brer-rabbit/zoxnoxious/vcv_rack/src/Zoxnoxious5524.cpp

#include "TurnsCountingKnob.hpp"
#include "Zoxnoxious5524.hpp"

namespace zox {

// VCO1 ==> SSI2130
// VCO2 ==> AS3394

// these enums define the channel order being sent over the wire
enum cvChannel {
    // DAC AS3394 / chip select 0
    VCO_MIX = 0,
    VCO_TWO_PW,
    FINAL_GAIN,
    VCO_TWO_TRI_VCF,
    VCF_RESONANCE,
    VCO_ONE_MOD_AMOUNT,
    VCO_TWO_VOCT,
    VCF_CUTOFF,
    // DAC SSI2130 / SPI chip select 1
    VCO_ONE_TRIANGLE,
    VCO_ONE_LINEAR,
    VCO_ONE_VOCT,
    VCO_ONE_PW,
    VCO_TWO_WAVESHAPE_TZFM,
    VCO_TWO_MOD_AMOUNT,
    VCO_ONE_PULSE,
    VCO_ONE_SAW
};



Zoxnoxious5524::Zoxnoxious5524() : output1NameString(invalidCardOutputName),
                               output2NameString(invalidCardOutputName),
                               buttonMidiController(buttonMappings),
                               routes{{
    {VCO_ONE_SAW_KNOB_PARAM, VCO_ONE_SAW_INPUT, VCO_ONE_SAW, 10.f, &vcoOneSawClipTimer, nullptr, CvOperation::MultiplyNormalled},
    {VCO_ONE_PULSE_KNOB_PARAM, VCO_ONE_PULSE_INPUT, VCO_ONE_PULSE, 10.f, &vcoOnePulseClipTimer, nullptr, CvOperation::MultiplyNormalled},
    {VCO_TWO_MOD_AMOUNT_KNOB_PARAM, VCO_TWO_MOD_AMOUNT_INPUT, VCO_TWO_MOD_AMOUNT, 10.f, &vcoTwoModAmountClipTimer, nullptr, CvOperation::Add},
    {VCO_TWO_WAVESHAPE_TZFM_KNOB_PARAM, VCO_TWO_WAVESHAPE_TZFM_INPUT, VCO_TWO_WAVESHAPE_TZFM, 10.f, &vcoTwoWaveshapeTzfmClipTimer, nullptr, CvOperation::Add},
    {VCO_ONE_PW_KNOB_PARAM,VCO_ONE_PW_INPUT, VCO_ONE_PW, 10.f, &vcoOnePwClipTimer, nullptr, CvOperation::Add},
    {VCO_ONE_VOCT_KNOB_PARAM, VCO_ONE_VOCT_INPUT, VCO_ONE_VOCT, 8.f, &vcoOneVoctClipTimer, nullptr, CvOperation::Add},
    {VCO_ONE_LINEAR_KNOB_PARAM, VCO_ONE_LINEAR_INPUT, VCO_ONE_LINEAR, 10.f, &vcoOneLinearClipTimer, nullptr, CvOperation::Add},
    {VCO_ONE_TRIANGLE_KNOB_PARAM, VCO_ONE_TRIANGLE_INPUT, VCO_ONE_TRIANGLE, 10.f, &vcoOneTriangleClipTimer, nullptr, CvOperation::MultiplyNormalled},
    {VCF_CUTOFF_KNOB_PARAM,VCF_CUTOFF_INPUT, VCF_CUTOFF, 10.f, &vcfCutoffClipTimer, nullptr, CvOperation::Add},
    {VCO_TWO_VOCT_KNOB_PARAM, VCO_TWO_VOCT_INPUT, VCO_TWO_VOCT, 6.f, &vcoTwoVoctClipTimer, nullptr, CvOperation::Add},
    {VCO_ONE_MOD_AMOUNT_KNOB_PARAM, VCO_ONE_MOD_AMOUNT_INPUT, VCO_ONE_MOD_AMOUNT, 10.f, &vcoOneModAmountClipTimer, nullptr, CvOperation::Add},
    {VCF_RESONANCE_KNOB_PARAM, VCF_RESONANCE_INPUT, VCF_RESONANCE, 10.f, &vcfResonanceClipTimer, dualLinearSwitch0_8, CvOperation::Add},
    {VCO_TWO_TRI_VCF_KNOB_PARAM, VCO_TWO_TRI_VCF_INPUT, VCO_TWO_TRI_VCF, 10.f, &vcoTwoTriVcfClipTimer, nullptr, CvOperation::Add},
    {FINAL_GAIN_KNOB_PARAM, FINAL_GAIN_INPUT, FINAL_GAIN, 10.f, &finalGainClipTimer, nullptr, CvOperation::Add},
    {VCO_TWO_PW_KNOB_PARAM,VCO_TWO_PW_INPUT, VCO_TWO_PW, 10.f, &vcoTwoPwClipTimer, nullptr, CvOperation::Add},
    {VCO_MIX_KNOB_PARAM, VCO_MIX_INPUT, VCO_MIX, 10.f, &vcoMixClipTimer, nullptr, CvOperation::Add} }} {

  setParticipant(this);
  setLightEnum(LINK_STATUS_LIGHT);

  config(PARAMS_LEN, INPUTS_LEN, OUTPUTS_LEN, LIGHTS_LEN);
  configParam(VCO_ONE_VOCT_KNOB_PARAM, 0.f, 1.f, 0.5f, "Frequency", " V", 0.f, 8.f);
  configParam(VCO_ONE_PW_KNOB_PARAM, 0.f, 1.f, 0.5f, "Pulse Width", "%", 0.f, 100.f);
  configParam(VCO_ONE_LINEAR_KNOB_PARAM, 0.f, 1.f, 0.5f, "Linear Mod", " V", 0.f, 10.f -5.f);
  configParam(VCO_TWO_VOCT_KNOB_PARAM, 0.f, 1.f, 0.5f, "Frequency", " V", 0.f, 6.f);
  configParam(VCO_TWO_PW_KNOB_PARAM, 0.f, 1.f, 0.5f, "Pulse Width", "%", 0.f, 100.f);
  configParam(VCF_CUTOFF_KNOB_PARAM, 0.f, 1.f, 1.f, "Cutoff", " V", 0.f, 10.f, -1.f);
  configParam(VCF_RESONANCE_KNOB_PARAM, 0.f, 1.f, 0.f, "Resonance", "%", 0.f, 100.f);
  configParam(VCO_MIX_KNOB_PARAM, 0.f, 1.f, 0.5f, "VCO1/VCO2 Mix", "%", 0.f, 200.f, -100.f);
  configParam(FINAL_GAIN_KNOB_PARAM, 0.f, 1.f, 0.f, "Final VCA", "%", 0.f, 100.f);
  configParam(VCO_ONE_PULSE_KNOB_PARAM, 0.f, 1.f, 0.f, "Pulse Gain", "%", 0.f, 100.f);
  configParam(VCO_ONE_TRIANGLE_KNOB_PARAM, 0.f, 1.f, 1.f, "Tri Gain", "%", 0.f, 100.f);
  configParam(VCO_ONE_SAW_KNOB_PARAM, 0.f, 1.f, 0.f, "Saw Gain", "%", 0.f, 100.f);

  configParam(VCO_ONE_MOD_AMOUNT_KNOB_PARAM, 0.f, 1.f, 0.f, "Mod Amount", "%", 0.f, 100.f);
  configParam(VCO_TWO_MOD_AMOUNT_KNOB_PARAM, 0.f, 1.f, 0.f, "Mod Amount", "%", 0.f, 100.f);
  configParam(VCO_TWO_WAVESHAPE_TZFM_KNOB_PARAM, 0.f, 1.f, 0.f, "Waveshape TZFM", "%", 0.f, 100.f);
  configParam(VCO_TWO_TRI_VCF_KNOB_PARAM, 0.f, 1.f, 0.f, "Tri to VCF", "%", 0.f, 100.f);

  configSwitch(VCO_ONE_TO_EXP_FM_VCO_TWO_BUTTON_PARAM, 0.f, 1.f, 0.f, "VCO One to Exp FM VCO Two", {"Off", "On"});
  configSwitch(VCO_ONE_TO_WAVE_SELECT_VCO_TWO_BUTTON_PARAM, 0.f, 1.f, 0.f, "VCO One to Wave Select VCO Two", {"Off", "On"});

  configSwitch(VCO_TWO_TO_FREQ_VCO_ONE_BUTTON_PARAM, 0.f, 1.f, 0.f, "VCO Two to TZ-FM VCO One", {"Off", "On"});
  configSwitch(VCO_TWO_TO_SOFT_SYNC_VCO_ONE_BUTTON_PARAM, 0.f, 1.f, 0.f, "Soft Sync VCO One from VCO Two", {"Off", "On"});
  configSwitch(VCO_TWO_TO_HARD_SYNC_VCO_ONE_BUTTON_PARAM, 0.f, 1.f, 0.f, "Hard Sub Sync VCO One from VCO Two", {"Off", "On"});

  configSwitch(VCO_ONE_TO_PW_VCO_TWO_BUTTON_PARAM, 0.f, 1.f, 0.f, "VCO One to VCO Two Pulse Width", {"Off", "On"});
  configSwitch(VCO_ONE_TO_VCF_BUTTON_PARAM, 0.f, 1.f, 0.f, "VCO One to VCF Freq Cutoff", {"Off", "On"});
  configSwitch(VCO_TWO_TO_PW_VCO_ONE_BUTTON_PARAM, 0.f, 1.f, 0.f, "VCO Two to VCO One Pulse Width", {"Off", "On"});

  configSwitch(VCO_TWO_WAVE_PULSE_BUTTON_PARAM, 0.f, 1.f, 0.f, "VCO Two Pulse Enable", {"Off", "On"});
  configSwitch(VCO_TWO_WAVE_SAW_BUTTON_PARAM, 0.f, 1.f, 0.f, "VCO Two Sawtooth Enable", {"Off", "On"});
  configSwitch(VCO_TWO_WAVE_TRI_BUTTON_PARAM, 0.f, 1.f, 0.f, "VCO Two Triangle Enable", {"Off", "On"});

  configInput(VCO_ONE_VOCT_INPUT, "VCO One V/Oct");
  configInput(VCO_ONE_PW_INPUT, "VCO One Pulse Width");
  configInput(VCO_ONE_LINEAR_INPUT, "VCO One Linear Freq Mod");
  configInput(VCO_TWO_VOCT_INPUT, "VCO Two V/Oct");
  configInput(VCO_TWO_PW_INPUT, "VCO Two Pulse Width");
  configInput(VCF_CUTOFF_INPUT, "VCF Cutoff Frequency");
  configInput(VCF_RESONANCE_INPUT, "VCF Resonance");
  configInput(VCO_MIX_INPUT, "VCO One / VCO Two Mix");
  configInput(FINAL_GAIN_INPUT, "Final VCA Gain");
  configInput(VCO_ONE_PULSE_INPUT, "VCO One Pulse Level");
  configInput(VCO_ONE_TRIANGLE_INPUT, "VCO One Triangle Level");
  configInput(VCO_ONE_SAW_INPUT, "VCO One Sawtooth Level");
  configInput(VCO_ONE_MOD_AMOUNT_INPUT, "VCO One Mod Level");
  configInput(VCO_TWO_MOD_AMOUNT_INPUT, "VCO Two Mod Level");
  configInput(VCO_TWO_WAVESHAPE_TZFM_INPUT, "VCO Two Waveshape to VCO One TZFM");
  configInput(VCO_TWO_TRI_VCF_INPUT, "VCO Two Triangle to VCF Cutoff Frequency");

  output1NameString.reserve(16);
  output2NameString.reserve(16);
}


void Zoxnoxious5524::pullSamples(const rack::engine::Module::ProcessArgs &args, dsp::Frame<maxAudioChannels> &sharedFrame, int offset) {
  const float clipTime = 0.25f;

  // match the channels to what the Pi expects on the other side and it's all good
  processCvRoutes(routes.data(),
                  routes.size(),
                  clipTime,
                  offset,
                  sharedFrame.samples,
                  params.data(),
                  inputs.data());

  // VCO Two PW
  // Note Pulse Width handles enable/disable
  vcoTwoPulseEnabled = static_cast<bool>(params[VCO_TWO_WAVE_PULSE_BUTTON_PARAM].getValue());
  if (vcoTwoPulseEnabled) {
    if (pwLimit) {
      sharedFrame.samples[offset + VCO_TWO_PW] = sharedFrame.samples[offset + VCO_TWO_PW] * 0.88f;
    }
  }
  else {
    sharedFrame.samples[offset + VCO_TWO_PW] = 1.f;
  }

  // graph weight info
  output1Weight = sharedFrame.samples[offset + FINAL_GAIN];
  output2Weight = std::max(sharedFrame.samples[offset + VCO_ONE_TRIANGLE],
                           std::max(sharedFrame.samples[offset + VCO_ONE_SAW],
                                    sharedFrame.samples[offset + VCO_ONE_PULSE]));

}


bool Zoxnoxious5524::pullMidi(const rack::engine::Module::ProcessArgs &args, uint32_t clockDivision, int midiChannel, midi::Message &midiMessage) {
  bool midiMsgSet = false;
  bool shapedOn = (params[VCO_TWO_WAVESHAPE_TZFM_KNOB_PARAM].getValue() + inputs[VCO_TWO_WAVESHAPE_TZFM_INPUT].getVoltage() / 10.f) > 0.f;
  bool tzfmDirectOn = params[VCO_TWO_TO_FREQ_VCO_ONE_BUTTON_PARAM].getValue() > 0.5f &&
    (params[VCO_TWO_MOD_AMOUNT_KNOB_PARAM].getValue() + inputs[VCO_TWO_MOD_AMOUNT_INPUT].getVoltage() / 10.f) > 0.f;

  // pullMidi runs at something better than display frame rate, so all UI visual stuff is here

  // the pulse doesn't send any midi-- it just allows or limits the pulse width
  if (params[VCO_TWO_WAVE_PULSE_BUTTON_PARAM].getValue() > 0.f) {
    lights[VCO_TWO_WAVE_PULSE_BUTTON_LIGHT].setBrightness(1.f);
    lights[TZFM_PULSE_STATUS_LIGHT].setBrightness( tzfmDirectOn ? 1.f : 0.25f );
    lights[WAVESHAPE_PULSE_STATUS_LIGHT].setBrightness( shapedOn ? 1.f : 0.25f );
  }
  else {
    lights[VCO_TWO_WAVE_PULSE_BUTTON_LIGHT].setBrightness(0.f);
    lights[TZFM_PULSE_STATUS_LIGHT].setBrightness(0.f);
    lights[WAVESHAPE_PULSE_STATUS_LIGHT].setBrightness(0.f);
  }

  int vcoTwoSaw;
  int vcoTwoTri;
  if (params[VCO_TWO_WAVE_SAW_BUTTON_PARAM].getValue() > 0.f) {
    vcoTwoSaw = 2;
    lights[VCO_TWO_WAVE_SAW_BUTTON_LIGHT].setBrightness(1.f);
    lights[TZFM_SAW_STATUS_LIGHT].setBrightness( tzfmDirectOn ? 1.f : 0.25f );
    lights[WAVESHAPE_HALFSINE_STATUS_LIGHT].setBrightness( shapedOn ? 1.f : 0.25f );
  } else {
    vcoTwoSaw = 0;
    lights[VCO_TWO_WAVE_SAW_BUTTON_LIGHT].setBrightness(0.f);
    lights[TZFM_SAW_STATUS_LIGHT].setBrightness(0.f);
    lights[WAVESHAPE_HALFSINE_STATUS_LIGHT].setBrightness(0.f);
  }

  if (params[VCO_TWO_WAVE_TRI_BUTTON_PARAM].getValue() > 0.f) {
    vcoTwoTri = 1;
    lights[VCO_TWO_WAVE_TRI_BUTTON_LIGHT].setBrightness(1.f);
    lights[TZFM_TRI_STATUS_LIGHT].setBrightness( tzfmDirectOn ? 1.f : 0.25f );
    lights[WAVESHAPE_SINE_STATUS_LIGHT].setBrightness( shapedOn ? 1.f : 0.25f );
  } else {
    vcoTwoTri = 0;
    lights[VCO_TWO_WAVE_TRI_BUTTON_LIGHT].setBrightness(0.f);
    lights[TZFM_TRI_STATUS_LIGHT].setBrightness(0.f);
    lights[WAVESHAPE_SINE_STATUS_LIGHT].setBrightness(0.f);
  }

  // convert the saw & tri params to the MIDI prog change number with four options
  int vcoTwoTriSawCurrentState = vcoTwoSaw + vcoTwoTri + vcoTwoSawTriMidiProgramOffset;
  if (vcoTwoTriSawCurrentState != vcoTwoTriSawPrevState) {
    vcoTwoTriSawPrevState = vcoTwoTriSawCurrentState;
    setMidiProgramChangeMessage(midiMessage, midiChannel, vcoTwoTriSawCurrentState);
    midiMsgSet = true;
  }


  // all buttons outside of the above selector are handled here
  if (!midiMsgSet) {
    midiMsgSet = buttonMidiController.process(this, midiChannel, midiMessage);
  }
  buttonMidiController.updateLights(this);


  // clipping lights and timers
  const float lightTime = args.sampleTime * clockDivision;
  const float brightnessDeltaTime = 1 / lightTime;

  vcoOneVoctClipTimer -= lightTime;
  lights[VCO_ONE_VOCT_CLIP_LIGHT].setBrightnessSmooth(vcoOneVoctClipTimer > 0.f, brightnessDeltaTime);

  vcoOnePwClipTimer -= lightTime;
  lights[VCO_ONE_PW_CLIP_LIGHT].setBrightnessSmooth(vcoOnePwClipTimer > 0.f, brightnessDeltaTime);

  vcoOneLinearClipTimer -= lightTime;
  lights[VCO_ONE_LINEAR_CLIP_LIGHT].setBrightnessSmooth(vcoOneLinearClipTimer > 0.f, brightnessDeltaTime);

  vcoTwoVoctClipTimer -= lightTime;
  lights[VCO_TWO_VOCT_CLIP_LIGHT].setBrightnessSmooth(vcoTwoVoctClipTimer > 0.f, brightnessDeltaTime);

  vcoTwoPwClipTimer -= lightTime;
  lights[VCO_TWO_PW_CLIP_LIGHT].setBrightnessSmooth(vcoTwoPwClipTimer > 0.f, brightnessDeltaTime);

  vcfCutoffClipTimer -= lightTime;
  lights[VCF_CUTOFF_CLIP_LIGHT].setBrightnessSmooth(vcfCutoffClipTimer > 0.f, brightnessDeltaTime);

  vcfResonanceClipTimer -= lightTime;
  lights[VCF_RESONANCE_CLIP_LIGHT].setBrightnessSmooth(vcfResonanceClipTimer > 0.f, brightnessDeltaTime);

  vcoMixClipTimer -= lightTime;
  lights[VCO_MIX_CLIP_LIGHT].setBrightnessSmooth(vcoMixClipTimer > 0.f, brightnessDeltaTime);

  finalGainClipTimer -= lightTime;
  lights[FINAL_GAIN_CLIP_LIGHT].setBrightnessSmooth(finalGainClipTimer > 0.f, brightnessDeltaTime);

  vcoOnePulseClipTimer -= lightTime;
  lights[VCO_ONE_PULSE_CLIP_LIGHT].setBrightnessSmooth(vcoOnePulseClipTimer > 0.f, brightnessDeltaTime);

  vcoOneTriangleClipTimer -= lightTime;
  lights[VCO_ONE_TRIANGLE_CLIP_LIGHT].setBrightnessSmooth(vcoOneTriangleClipTimer > 0.f, brightnessDeltaTime);

  vcoOneSawClipTimer -= lightTime;
  lights[VCO_ONE_SAW_CLIP_LIGHT].setBrightnessSmooth(vcoOneSawClipTimer > 0.f, brightnessDeltaTime);

  vcoOneModAmountClipTimer -= lightTime;
  lights[VCO_ONE_MOD_AMOUNT_CLIP_LIGHT].setBrightnessSmooth(vcoOneModAmountClipTimer > 0.f, brightnessDeltaTime);

  vcoTwoModAmountClipTimer -= lightTime;
  lights[VCO_TWO_MOD_AMOUNT_CLIP_LIGHT].setBrightnessSmooth(vcoTwoModAmountClipTimer > 0.f, brightnessDeltaTime);

  vcoTwoWaveshapeTzfmClipTimer -= lightTime;
  lights[VCO_TWO_WAVESHAPE_TZFM_CLIP_LIGHT].setBrightnessSmooth(vcoTwoWaveshapeTzfmClipTimer > 0.f, brightnessDeltaTime);

  vcoTwoTriVcfClipTimer -= lightTime;
  lights[VCO_TWO_TRI_VCF_CLIP_LIGHT].setBrightnessSmooth(vcoTwoTriVcfClipTimer > 0.f, brightnessDeltaTime);

  return midiMsgSet;
}


  /** getCardHardwareId
   * return the hardware Id of the card
   */
static const uint8_t hardwareId = 0x04;
uint8_t Zoxnoxious5524::getHardwareId() const {
  return hardwareId;
}


bool Zoxnoxious5524::pullGraphInfo(ParticipantGraphInfo& info) {
  info.moduleId = getId();
  info.hardwareId = hardwareId;
  info.slotNum = lifecycle.slotNum;
  info.source1.valid = false;
  info.source2.valid = false;
  info.output1Weight = output1Weight;
  info.output2Weight = output2Weight;
  return true;
}

  /* Participant interface: return Module identifier */
int64_t Zoxnoxious5524::getModuleId() {
  return getId();
}

void Zoxnoxious5524::onReset(const ResetEvent& e) {
  Module::onReset(e);
  pwLimit = 0;
}

void Zoxnoxious5524::onAttach() {
  if (lifecycle.nameService == nullptr) {
    return;
  }
  auto *ptr1 = lifecycle.nameService->getNamePtr(lifecycle.slotNum * 2);
  auto *ptr2 = lifecycle.nameService->getNamePtr(lifecycle.slotNum * 2 + 1);
  output1NameString = ptr1 ? *ptr1 : invalidCardOutputName;
  output2NameString = ptr2 ? *ptr2 : invalidCardOutputName;
}


json_t* Zoxnoxious5524::dataToJson() {
  json_t* rootJ = json_object();
  json_object_set_new(rootJ, "pwLimit", json_integer(pwLimit));
  return rootJ;
}

void Zoxnoxious5524::dataFromJson(json_t* rootJ) {
  json_t* pwLimitJ = json_object_get(rootJ, "pwLimit");
  if (pwLimitJ) {
    pwLimit = json_integer_value(pwLimitJ);
  }
}


CouplingDisplayState Zoxnoxious5524::getCouplingDisplayState() {
  CouplingDisplayState couplingState;

  // bizlogic to identify what is modulating what
  couplingState.vco2RawToVco1Tzfm = params[VCO_TWO_TO_FREQ_VCO_ONE_BUTTON_PARAM].getValue() > 0.f ?
    (inputs[VCO_TWO_MOD_AMOUNT_INPUT].getVoltage() / 10.f) + params[VCO_TWO_MOD_AMOUNT_KNOB_PARAM].getValue() : 0.f;

  couplingState.vco2ShapedToVco1Tzfm = (inputs[VCO_TWO_WAVESHAPE_TZFM_INPUT].getVoltage() / 10.f) +
    params[VCO_TWO_WAVESHAPE_TZFM_KNOB_PARAM].getValue();

  couplingState.vco2RawWaveMask =
    (params[VCO_TWO_WAVE_PULSE_BUTTON_PARAM].getValue() ? RAW_PULSE : 0) |
    (params[VCO_TWO_WAVE_SAW_BUTTON_PARAM].getValue() ? RAW_SAW : 0) |
    (params[VCO_TWO_WAVE_TRI_BUTTON_PARAM].getValue() ? RAW_TRI : 0);
  couplingState.vco2ShapedWaveMask = couplingState.vco2RawWaveMask;

  couplingState.vco1ToVco2ExpFm = params[VCO_ONE_TO_EXP_FM_VCO_TWO_BUTTON_PARAM].getValue() > 0.f ?
    (inputs[VCO_ONE_MOD_AMOUNT_INPUT].getVoltage() / 10.f) + params[VCO_ONE_MOD_AMOUNT_KNOB_PARAM].getValue() : 0.f;
  couplingState.vco1ToVcfExpFm = params[VCO_ONE_TO_VCF_BUTTON_PARAM].getValue() > 0.f ?
    (inputs[VCO_ONE_MOD_AMOUNT_INPUT].getVoltage() / 10.f) + params[VCO_ONE_MOD_AMOUNT_KNOB_PARAM].getValue() : 0.f;
  couplingState.vco2ToVcfLinFm = (inputs[VCO_TWO_TRI_VCF_INPUT].getVoltage() / 10.f) + params[VCO_TWO_TRI_VCF_KNOB_PARAM].getValue();

  couplingState.syncHardSub = params[VCO_TWO_TO_HARD_SYNC_VCO_ONE_BUTTON_PARAM].getValue() > 0.f;
  couplingState.syncSoft = params[VCO_TWO_TO_SOFT_SYNC_VCO_ONE_BUTTON_PARAM].getValue() > 0.f;

  // TODO: treat this like other vco1 to vco2 modulations
  couplingState.vco1ToVco2WaveSelect = params[VCO_ONE_TO_WAVE_SELECT_VCO_TWO_BUTTON_PARAM].getValue() > 0.f;

  return couplingState;        
}


struct Zoxnoxious5524Widget : ModuleWidget {
  Zoxnoxious5524Widget(Zoxnoxious5524* module) {
    setModule(module);
    setPanel(createPanel(asset::plugin(pluginInstance, "res/Zoxnoxious5524.svg")));

    addChild(createWidget<ScrewSlottedKnurled>(Vec(RACK_GRID_WIDTH, 0)));
    addChild(createWidget<ScrewSlottedKnurled>(Vec(box.size.x - 2 * RACK_GRID_WIDTH, 0)));
    addChild(createWidget<ScrewSlottedKnurled>(Vec(RACK_GRID_WIDTH, RACK_GRID_HEIGHT - RACK_GRID_WIDTH)));
    addChild(createWidget<ScrewSlottedKnurled>(Vec(box.size.x - 2 * RACK_GRID_WIDTH, RACK_GRID_HEIGHT - RACK_GRID_WIDTH)));

    auto* knobVco1 = createParamCentered<TurnsCountingKnob>(
      mm2px(Vec(14.165, 28.323)),   // centre position on panel (mm)
      module,
      Zoxnoxious5524::VCO_ONE_VOCT_KNOB_PARAM);
    knobVco1->setTurns(8);
    addParam(knobVco1);

    addParam(createParamCentered<ZoxMediumKnob>(mm2px(Vec(14.165, 62.445)), module, Zoxnoxious5524::VCO_ONE_PW_KNOB_PARAM));
    addParam(createParamCentered<ZoxSmallKnob>(mm2px(Vec(34.334, 28.323)), module, Zoxnoxious5524::VCO_ONE_LINEAR_KNOB_PARAM));

    addParam(createParamCentered<ZoxSmallKnob>(mm2px(Vec(9.677, 99.187)), module, Zoxnoxious5524::VCO_ONE_PULSE_KNOB_PARAM));
    addParam(createParamCentered<ZoxSmallKnob>(mm2px(Vec(34.334, 99.187)), module, Zoxnoxious5524::VCO_ONE_TRIANGLE_KNOB_PARAM));
    addParam(createParamCentered<ZoxSmallKnob>(mm2px(Vec(22.0, 99.187)), module, Zoxnoxious5524::VCO_ONE_SAW_KNOB_PARAM));

    auto* knobVco2 = createParamCentered<TurnsCountingKnob>(
      mm2px(Vec(84.5, 28.323)),
      module,
      Zoxnoxious5524::VCO_TWO_VOCT_KNOB_PARAM);
    knobVco2->setTurns(6);
    addParam(knobVco2);
    addParam(createParamCentered<ZoxMediumKnob>(mm2px(Vec(84.5, 62.445)), module, Zoxnoxious5524::VCO_TWO_PW_KNOB_PARAM));

    auto* knobVCF = createParamCentered<TurnsCountingKnob>(
      mm2px(Vec(174.5, 28.445)),
      module,
      Zoxnoxious5524::VCF_CUTOFF_KNOB_PARAM);
    knobVCF->setTurns(10);
    addParam(knobVCF);

    addParam(createParamCentered<ZoxSmallKnob>(mm2px(Vec(168.104, 62.445)), module, Zoxnoxious5524::VCF_RESONANCE_KNOB_PARAM));
    addParam(createParamCentered<ZoxSmallKnob>(mm2px(Vec(77.294, 109.97)), module, Zoxnoxious5524::VCO_MIX_KNOB_PARAM));
    addParam(createParamCentered<ZoxLargeKnob>(mm2px(Vec(174.5, 96.503)), module, Zoxnoxious5524::FINAL_GAIN_KNOB_PARAM));

      
    addParam(createParamCentered<ZoxSmallKnob>(mm2px(Vec(54.5, 28.323)), module, Zoxnoxious5524::VCO_ONE_MOD_AMOUNT_KNOB_PARAM));
    addParam(createParamCentered<ZoxSmallKnob>(mm2px(Vec(116.5, 28.323)), module, Zoxnoxious5524::VCO_TWO_MOD_AMOUNT_KNOB_PARAM));

    addParam(createParamCentered<ZoxSmallKnob>(mm2px(Vec(144.5, 45.915)), module, Zoxnoxious5524::VCO_TWO_WAVESHAPE_TZFM_KNOB_PARAM));
    addParam(createParamCentered<ZoxSmallKnob>(mm2px(Vec(110.451, 84.995)), module, Zoxnoxious5524::VCO_TWO_TRI_VCF_KNOB_PARAM));

    addParam(createLightParamCentered<ZPushButtonMediumStatefulLightLatch<SmallSimpleLight<ZoxAmberLight>>>(mm2px(Vec(74.202, 91.587)), module, Zoxnoxious5524::VCO_TWO_WAVE_PULSE_BUTTON_PARAM, Zoxnoxious5524::VCO_TWO_WAVE_PULSE_BUTTON_LIGHT));
    addParam(createLightParamCentered<ZPushButtonMediumStatefulLightLatch<SmallSimpleLight<ZoxAmberLight>>>(mm2px(Vec(84.5, 91.587)), module, Zoxnoxious5524::VCO_TWO_WAVE_SAW_BUTTON_PARAM, Zoxnoxious5524::VCO_TWO_WAVE_SAW_BUTTON_LIGHT));
    addParam(createLightParamCentered<ZPushButtonMediumStatefulLightLatch<SmallSimpleLight<ZoxAmberLight>>>(mm2px(Vec(94.798, 91.587)), module, Zoxnoxious5524::VCO_TWO_WAVE_TRI_BUTTON_PARAM, Zoxnoxious5524::VCO_TWO_WAVE_TRI_BUTTON_LIGHT));


    addParam(createLightParamCentered<ZPushButtonMediumStatefulLightLatch<SmallSimpleLight<ZoxAmberLight>>>(mm2px(Vec(54.5, 57.677)), module, Zoxnoxious5524::VCO_ONE_TO_EXP_FM_VCO_TWO_BUTTON_PARAM, Zoxnoxious5524::VCO_ONE_TO_EXP_FM_VCO_TWO_BUTTON_LIGHT));
    addParam(createLightParamCentered<ZPushButtonMediumStatefulLightLatch<SmallSimpleLight<ZoxAmberLight>>>(mm2px(Vec(54.5, 80.284)), module, Zoxnoxious5524::VCO_ONE_TO_WAVE_SELECT_VCO_TWO_BUTTON_PARAM, Zoxnoxious5524::VCO_ONE_TO_WAVE_SELECT_VCO_TWO_BUTTON_LIGHT));

    addParam(createLightParamCentered<ZPushButtonMediumStatefulLightLatch<SmallSimpleLight<ZoxAmberLight>>>(mm2px(Vec(116.5, 68.98)), module, Zoxnoxious5524::VCO_TWO_TO_FREQ_VCO_ONE_BUTTON_PARAM, Zoxnoxious5524::VCO_TWO_TO_FREQ_VCO_ONE_BUTTON_LIGHT));
    addParam(createLightParamCentered<ZPushButtonMediumStatefulLightLatch<SmallSimpleLight<ZoxAmberLight>>>(mm2px(Vec(54.5, 68.98)), module, Zoxnoxious5524::VCO_ONE_TO_PW_VCO_TWO_BUTTON_PARAM, Zoxnoxious5524::VCO_ONE_TO_PW_VCO_TWO_BUTTON_LIGHT));
    addParam(createLightParamCentered<ZPushButtonMediumStatefulLightLatch<SmallSimpleLight<ZoxAmberLight>>>(mm2px(Vec(54.5, 93.587)), module, Zoxnoxious5524::VCO_ONE_TO_VCF_BUTTON_PARAM, Zoxnoxious5524::VCO_ONE_TO_VCF_BUTTON_LIGHT));
    addParam(createLightParamCentered<ZPushButtonMediumStatefulLightLatch<SmallSimpleLight<ZoxAmberLight>>>(mm2px(Vec(116.5, 57.78)), module, Zoxnoxious5524::VCO_TWO_TO_PW_VCO_ONE_BUTTON_PARAM, Zoxnoxious5524::VCO_TWO_TO_PW_VCO_ONE_BUTTON_LIGHT));

    addParam(createLightParamCentered<ZPushButtonMediumStatefulLightLatch<SmallSimpleLight<ZoxAmberLight>>>(mm2px(Vec(116.5, 100.698)), module, Zoxnoxious5524::VCO_TWO_TO_SOFT_SYNC_VCO_ONE_BUTTON_PARAM, Zoxnoxious5524::VCO_TWO_TO_SOFT_SYNC_VCO_ONE_BUTTON_LIGHT));
    addParam(createLightParamCentered<ZPushButtonMediumStatefulLightLatch<SmallSimpleLight<ZoxAmberLight>>>(mm2px(Vec(116.5, 111.882)), module, Zoxnoxious5524::VCO_TWO_TO_HARD_SYNC_VCO_ONE_BUTTON_PARAM, Zoxnoxious5524::VCO_TWO_TO_HARD_SYNC_VCO_ONE_BUTTON_LIGHT));

    addInput(createInputCentered<BNCPort>(mm2px(Vec(14.165, 42.323)), module, Zoxnoxious5524::VCO_ONE_VOCT_INPUT));
    addInput(createInputCentered<BNCPort>(mm2px(Vec(14.165, 76.445)), module, Zoxnoxious5524::VCO_ONE_PW_INPUT));
    addInput(createInputCentered<BNCPort>(mm2px(Vec(34.334, 42.323)), module, Zoxnoxious5524::VCO_ONE_LINEAR_INPUT));
    addInput(createInputCentered<BNCPort>(mm2px(Vec(9.677, 111.55)), module, Zoxnoxious5524::VCO_ONE_PULSE_INPUT));
    addInput(createInputCentered<BNCPort>(mm2px(Vec(34.334, 111.55)), module, Zoxnoxious5524::VCO_ONE_TRIANGLE_INPUT));
    addInput(createInputCentered<BNCPort>(mm2px(Vec(22.0, 111.55)), module, Zoxnoxious5524::VCO_ONE_SAW_INPUT));

    addInput(createInputCentered<BNCPort>(mm2px(Vec(84.5, 42.323)), module, Zoxnoxious5524::VCO_TWO_VOCT_INPUT));
    addInput(createInputCentered<BNCPort>(mm2px(Vec(84.5, 76.445)), module, Zoxnoxious5524::VCO_TWO_PW_INPUT));

    addInput(createInputCentered<BNCPort>(mm2px(Vec(174.5, 42.323)), module, Zoxnoxious5524::VCF_CUTOFF_INPUT));
    addInput(createInputCentered<BNCPort>(mm2px(Vec(180.796, 62.445)), module, Zoxnoxious5524::VCF_RESONANCE_INPUT));
    addInput(createInputCentered<BNCPort>(mm2px(Vec(91.986, 109.97)), module, Zoxnoxious5524::VCO_MIX_INPUT));
    addInput(createInputCentered<BNCPort>(mm2px(Vec(174.5, 110.97)), module, Zoxnoxious5524::FINAL_GAIN_INPUT));

    addInput(createInputCentered<BNCPort>(mm2px(Vec(54.5, 42.323)), module, Zoxnoxious5524::VCO_ONE_MOD_AMOUNT_INPUT));
    addInput(createInputCentered<BNCPort>(mm2px(Vec(116.5, 42.323)), module, Zoxnoxious5524::VCO_TWO_MOD_AMOUNT_INPUT));
    addInput(createInputCentered<BNCPort>(mm2px(Vec(144.5, 59.915)), module, Zoxnoxious5524::VCO_TWO_WAVESHAPE_TZFM_INPUT));
    addInput(createInputCentered<BNCPort>(mm2px(Vec(123.143, 84.995)), module, Zoxnoxious5524::VCO_TWO_TRI_VCF_INPUT));

    addChild(createLightCentered<SmallLight<RedGreenBlueLight>>(mm2px(Vec(4.8, 121.586)), module, Zoxnoxious5524::LINK_STATUS_LIGHT));

    addChild(createLightCentered<SmallLight<ZoxAmberLight>>(mm2px(Vec(149.537, 90.673)), module, Zoxnoxious5524::TZFM_PULSE_STATUS_LIGHT));
    addChild(createLightCentered<SmallLight<ZoxAmberLight>>(mm2px(Vec(149.537, 84.673)), module, Zoxnoxious5524::TZFM_SAW_STATUS_LIGHT));
    addChild(createLightCentered<SmallLight<ZoxAmberLight>>(mm2px(Vec(149.537, 78.673)), module, Zoxnoxious5524::TZFM_TRI_STATUS_LIGHT));
    addChild(createLightCentered<SmallLight<ZoxAmberLight>>(mm2px(Vec(148.537, 35.378)), module, Zoxnoxious5524::WAVESHAPE_PULSE_STATUS_LIGHT));
    addChild(createLightCentered<SmallLight<ZoxAmberLight>>(mm2px(Vec(148.537, 29.378)), module, Zoxnoxious5524::WAVESHAPE_HALFSINE_STATUS_LIGHT));
    addChild(createLightCentered<SmallLight<ZoxAmberLight>>(mm2px(Vec(148.537, 23.378)), module, Zoxnoxious5524::WAVESHAPE_SINE_STATUS_LIGHT));

    addChild(createLightCentered<SmallLight<RedLight>>(mm2px(Vec(21.645, 37.112)), module, Zoxnoxious5524::VCO_ONE_VOCT_CLIP_LIGHT));
    addChild(createLightCentered<SmallLight<RedLight>>(mm2px(Vec(23.145, 71.234)), module, Zoxnoxious5524::VCO_ONE_PW_CLIP_LIGHT));
    addChild(createLightCentered<SmallLight<RedLight>>(mm2px(Vec(92.5, 37.112)), module, Zoxnoxious5524::VCO_TWO_VOCT_CLIP_LIGHT));
    addChild(createLightCentered<SmallLight<RedLight>>(mm2px(Vec(94.0, 71.234)), module, Zoxnoxious5524::VCO_TWO_PW_CLIP_LIGHT));
    addChild(createLightCentered<SmallLight<RedLight>>(mm2px(Vec(181.7, 36.961)), module, Zoxnoxious5524::VCF_CUTOFF_CLIP_LIGHT));
/*
  addChild(createLightCentered<SmallLight<RedLight>>(mm2px(Vec(84.5, 114.5)), module, Zoxnoxious5524::VCO_MIX_CLIP_LIGHT));
  addChild(createLightCentered<MediumLight<RedLight>>(mm2px(Vec(151.507, 31.798)), module, Zoxnoxious5524::VCF_RESONANCE_CLIP_LIGHT));
  addChild(createLightCentered<MediumLight<RedLight>>(mm2px(Vec(151.507, 56.411)), module, Zoxnoxious5524::FINAL_GAIN_CLIP_LIGHT));
  addChild(createLightCentered<MediumLight<RedLight>>(mm2px(Vec(16.261, 71.704)), module, Zoxnoxious5524::VCO_ONE_PULSE_CLIP_LIGHT));
  addChild(createLightCentered<MediumLight<RedLight>>(mm2px(Vec(53.608, 71.593)), module, Zoxnoxious5524::VCO_ONE_TRIANGLE_CLIP_LIGHT));
  addChild(createLightCentered<MediumLight<RedLight>>(mm2px(Vec(35.866, 71.867)), module, Zoxnoxious5524::VCO_ONE_SAW_CLIP_LIGHT));
  addChild(createLightCentered<MediumLight<RedLight>>(mm2px(Vec(16.668, 108.585)), module, Zoxnoxious5524::VCO_ONE_MOD_AMOUNT_CLIP_LIGHT));
  addChild(createLightCentered<MediumLight<RedLight>>(mm2px(Vec(77.188, 109.172)), module, Zoxnoxious5524::VCO_TWO_MOD_AMOUNT_CLIP_LIGHT));
  addChild(createLightCentered<MediumLight<RedLight>>(mm2px(Vec(131.902, 109.172)), module, Zoxnoxious5524::VCO_TWO_WAVESHAPE_TZFM_CLIP_LIGHT));
  addChild(createLightCentered<MediumLight<RedLight>>(mm2px(Vec(151.008, 109.286)), module, Zoxnoxious5524::VCO_TWO_TRI_VCF_CLIP_LIGHT));
*/

    mix1OutputTextField = createWidget<CardTextDisplay>(mm2px(Vec(163.5, 84.414)));
    mix1OutputTextField->setNumChars(13);
    mix1OutputTextField->box.size = (mm2px(Vec(21.0, 3.136)));
    mix1OutputTextField->setText(module ? &module->output1NameString : NULL);
    addChild(mix1OutputTextField);

    mix2OutputTextField = createWidget<CardTextDisplay>(mm2px(Vec(11.582, 84.481)));
    mix2OutputTextField->setNumChars(11);
    mix2OutputTextField->box.size = (mm2px(Vec(19.0, 3.136)));
    mix2OutputTextField->setText(module ? &module->output2NameString : NULL);
    addChild(mix2OutputTextField);

  }

  void appendContextMenu(Menu* menu) override {
    Zoxnoxious5524* module = getModule<Zoxnoxious5524>();
    menu->addChild(new MenuSeparator);
    menu->addChild(createIndexPtrSubmenuItem("Pulse Width", {"Allow DC", "Limit"}, &module->pwLimit));

    InstantiateExpanderItem *expanderItem = createMenuItem<InstantiateExpanderItem>("Add visualizer (right side)", "");
    expanderItem->module = module;
    expanderItem->model = modelZoxnoxious5524Visual;
    expanderItem->posit = box.pos;
    expanderItem->posit.x += box.size.x;
    menu->addChild(expanderItem);
  }

  CardTextDisplay *mix1OutputTextField;
  CardTextDisplay *mix2OutputTextField;
};


const std::vector<ButtonMapping<Zoxnoxious5524> > Zoxnoxious5524::buttonMappings = {
  { VCO_ONE_TO_EXP_FM_VCO_TWO_BUTTON_PARAM, VCO_ONE_TO_EXP_FM_VCO_TWO_BUTTON_LIGHT, {4,5} },
  { VCO_ONE_TO_WAVE_SELECT_VCO_TWO_BUTTON_PARAM, VCO_ONE_TO_WAVE_SELECT_VCO_TWO_BUTTON_LIGHT, {6,7} },
  { VCO_TWO_TO_FREQ_VCO_ONE_BUTTON_PARAM, VCO_TWO_TO_FREQ_VCO_ONE_BUTTON_LIGHT, {8,9} },
  { VCO_TWO_TO_SOFT_SYNC_VCO_ONE_BUTTON_PARAM, VCO_TWO_TO_SOFT_SYNC_VCO_ONE_BUTTON_LIGHT, {10,11 } },
  { VCO_ONE_TO_PW_VCO_TWO_BUTTON_PARAM, VCO_ONE_TO_PW_VCO_TWO_BUTTON_LIGHT, {12,13} },
  { VCO_ONE_TO_VCF_BUTTON_PARAM, VCO_ONE_TO_VCF_BUTTON_LIGHT, {14,15} },
  { VCO_TWO_TO_PW_VCO_ONE_BUTTON_PARAM, VCO_TWO_TO_PW_VCO_ONE_BUTTON_LIGHT, {16,17 } },
  { VCO_TWO_TO_HARD_SYNC_VCO_ONE_BUTTON_PARAM, VCO_TWO_TO_HARD_SYNC_VCO_ONE_BUTTON_LIGHT, {18,19 } }
};


} // namespace zox


Model* modelZoxnoxious5524 = createModel<zox::Zoxnoxious5524, zox::Zoxnoxious5524Widget>("Zoxnoxious5524");
