brer-rabbit/zoxnoxious/vcv_rack/src/OutputInterface.cpp

#include "plugin.hpp"

#include "OutputInterface.hpp"
#include "constants.hpp"
#include "zcomponentlib.hpp"

namespace zox {

std::atomic<OutputInterface*> OutputInterface::instance { nullptr };

static constexpr int midiPollRateHz = 100;
static constexpr int graphPollRateHz = 30;

enum cvChannel {
    OUT2_CHANNEL = 0,
    OUT1_CHANNEL
};


OutputInterface::OutputInterface() : out1LevelClipTimer(0.f),
                     out2LevelClipTimer(0.f),
                     buttonStates(buttonMappings.size()),
                     buttonMidiController(buttonMappings),
                     routes{
  {
    {OUT1_LEVEL_KNOB_PARAM, OUT1_LEVEL_INPUT, OUT1_CHANNEL, 10.f, &out1LevelClipTimer, nullptr, CvOperation::Add},
    {OUT2_LEVEL_KNOB_PARAM, OUT2_LEVEL_INPUT, OUT2_CHANNEL, 10.f, &out2LevelClipTimer, nullptr, CvOperation::Add}
  }}
{
  for(int i = 0; i < maxAudioDevices; ++i) {
    audioPorts.push_back(new ZoxnoxiousAudioPort(this));
  }

  config(PARAMS_LEN, INPUTS_LEN, OUTPUTS_LEN, LIGHTS_LEN);
  configParam(OUT1_LEVEL_KNOB_PARAM, 0.f, 1.f, 0.5f, "Out1 Level", " V", 0.f, 10.f);
  configParam(OUT2_LEVEL_KNOB_PARAM, 0.f, 1.f, 0.5f, "Out2 Level", " V", 0.f, 10.f);

  configSwitch(CARD_A_MIX1_OUTPUT_BUTTON_PARAM, 0.f, 1.f, 0.f, "Card A Out 1 to Audio Out");
  configSwitch(CARD_A_MIX2_OUTPUT_BUTTON_PARAM, 0.f, 1.f, 0.f, "Card A Out 2 to Audio Out");
  configSwitch(CARD_B_MIX1_OUTPUT_BUTTON_PARAM, 0.f, 1.f, 0.f, "Card B Out 1 to Audio Out");
  configSwitch(CARD_B_MIX2_OUTPUT_BUTTON_PARAM, 0.f, 1.f, 0.f, "Card B Out 2 to Audio Out");
  configSwitch(CARD_C_MIX1_OUTPUT_BUTTON_PARAM, 0.f, 1.f, 0.f, "Card C Out 1 to Audio Out");
  configSwitch(CARD_C_MIX2_OUTPUT_BUTTON_PARAM, 0.f, 1.f, 0.f, "Card C Out 2 to Audio Out");
  configSwitch(CARD_D_MIX1_OUTPUT_BUTTON_PARAM, 0.f, 1.f, 0.f, "Card D Out 1 to Audio Out");
  configSwitch(CARD_D_MIX2_OUTPUT_BUTTON_PARAM, 0.f, 1.f, 0.f, "Card D Out 2 to Audio Out");
  configSwitch(CARD_E_MIX1_OUTPUT_BUTTON_PARAM, 0.f, 1.f, 0.f, "Card E Out 1 to Audio Out");
  configSwitch(CARD_E_MIX2_OUTPUT_BUTTON_PARAM, 0.f, 1.f, 0.f, "Card E Out 2 to Audio Out");
  configSwitch(CARD_F_MIX1_OUTPUT_BUTTON_PARAM, 0.f, 1.f, 0.f, "Card F Out 1 to Audio Out");
  configSwitch(CARD_F_MIX2_OUTPUT_BUTTON_PARAM, 0.f, 1.f, 0.f, "Card F Out 2 to Audio Out");

  configInput(OUT1_LEVEL_INPUT, "Out1 VCA Level");
  configInput(OUT2_LEVEL_INPUT, "Out2 VCA Level");

  configLight(HARDWARE_LINK_LIGHT, "Connection Status");

  onReset();

  orchestrationClockDivider.setDivision(APP->engine->getSampleRate());  // once per second
  midiPollClockDivider.setDivision(static_cast<int>(APP->engine->getSampleRate()) / midiPollRateHz);
  graphPollClockDivider.setDivision(static_cast<int>(APP->engine->getSampleRate()) / graphPollRateHz);

  rightExpander.producerMessage = &graphMessages[0];
  rightExpander.consumerMessage = &graphMessages[1];
}


OutputInterface::~OutputInterface() {
  for (auto it = audioPorts.begin(); it != audioPorts.end(); ++it) {
    (*it)->setDriverId(-1);
    delete *it;
  }
}


void OutputInterface::onAdd(const AddEvent &e) {
  Module::onAdd(e);

  OutputInterface *expected = nullptr;
  OutputInterface::instance.compare_exchange_strong(expected, this, std::memory_order_release);
}


void OutputInterface::onRemove(const RemoveEvent &e) {
  OutputInterface *expected = this;
  OutputInterface::instance.compare_exchange_strong(expected, nullptr, std::memory_order_release);
  Module::onRemove(e);
}

void OutputInterface::onReset() {
  for (auto it = audioPorts.begin(); it != audioPorts.end(); ++it) {
    (*it)->setDriverId(-1);
  }
  midiOutput.reset();
}


void OutputInterface::onSampleRateChange(const SampleRateChangeEvent& e) {
  for (auto it = audioPorts.begin(); it != audioPorts.end(); ++it) {
    (*it)->engineInputBuffer.clear();
    (*it)->engineOutputBuffer.clear();
  }

  graphPollClockDivider.setDivision(static_cast<int>(e.sampleRate) / graphPollRateHz);
  midiPollClockDivider.setDivision(static_cast<int>(e.sampleRate) / midiPollRateHz);
  orchestrationClockDivider.setDivision(static_cast<int>(e.sampleRate));
}


// internal method for graph processing of source1/source2 (output nodes)
static void resolveGraphSource(const Broker::Snapshot& snap, GraphSource& source) {
  if (source.slotNum >= 0 && source.slotNum < maxVoiceCards) {
    const Slot& physical = snap.slots[source.slotNum];
    source.moduleId = physical.props.moduleId;
    source.hardwareId = physical.props.hardwareId;
    source.valid = physical.props.isAllocated && physical.props.moduleId;
  }
  else if (source.slotNum == maxVoiceCards) {
    // External input
    source.valid = true;
    source.moduleId = -1;
    source.hardwareId = invalidCardId;
  }
  else {
    source.valid = false;
    source.moduleId = -1;
    source.hardwareId = invalidCardId;
  }
}

// similar to previous- a helper for edges to the output
static GraphSource makeOutputGraphSource(const Broker::Snapshot& snap,
                                         int8_t slotNum,
                                         GraphPort port,
                                         float inputWeight) {
    GraphSource source;

    source.slotNum = slotNum;

    const Slot& physical = snap.slots[slotNum];
    source.moduleId = physical.props.moduleId;
    source.hardwareId = physical.props.hardwareId;

    source.port = port;
    source.valid = source.moduleId != -1;
    source.inputWeight = inputWeight;

    return source;
}



void OutputInterface::process(const ProcessArgs& args) {
  dsp::Frame<maxAudioChannels> sharedFrames[ audioPorts.size() ];
  bool isMidiClockTick = midiPollClockDivider.process();
  bool isOrchestrationClockTick = orchestrationClockDivider.process();
  bool isGraphPollClockTick = graphPollClockDivider.process();

  const Broker::Snapshot snap = broker.snapshot();

  // check for incoming midi
  midi::Message midiInMsg;
  while (midiInput.tryPop(&midiInMsg, args.frame)) {
    processMidiInMessage(midiInMsg);
  }

  // DEBUG REMOVE THIS
#define DEBUG_DISCO_REPORT
#ifdef DEBUG_DISCO_REPORT
  if (APP->engine->getFrame() == 40000) {
    midi::Message discoReport;
    discoReport.setSize(28);
    discoReport.bytes[0] = 0xF0;
    discoReport.bytes[1] = 0x7D;
    discoReport.bytes[2] = 0x01;
    discoReport.bytes[3] = 0x00; // change to 0x02 for 3340 VCO
    discoReport.bytes[4] = 0x00;
    discoReport.bytes[5] = 0x00;
    discoReport.bytes[6] = 0x02;
    discoReport.bytes[7] = 0x00;
    discoReport.bytes[8] = 0x00;
    discoReport.bytes[9] = 0x04;
    discoReport.bytes[10] = 0x00;
    discoReport.bytes[11] = 0x00;
    discoReport.bytes[12] = 0x06;
    discoReport.bytes[13] = 0x00;
    discoReport.bytes[14] = 0x00;
    discoReport.bytes[15] = 0x00;
    discoReport.bytes[16] = 0x00;
    discoReport.bytes[17] = 0x00;
    discoReport.bytes[18] = 0x03;
    discoReport.bytes[19] = 0x00;
    discoReport.bytes[20] = 0x00;
    discoReport.bytes[21] = 0x00;
    discoReport.bytes[22] = 0x00;
    discoReport.bytes[23] = 0x00;
    discoReport.bytes[24] = 0x07;
    discoReport.bytes[25] = 0x00;
    discoReport.bytes[26] = 0x00;
    processDiscoveryReport(discoReport);
  }
#endif

  if (discoveryReportReceived == false) {
    if (isOrchestrationClockTick) {
      INFO("Sending MIDI message discovery request");
      midiOutput.sendMidiMessage(MIDI_DISCOVERY_REQUEST_SYSEX);
    }
    return;
  }

  // walk the modules to see if anything should be attached
  if (isOrchestrationClockTick) {
    serviceParticipantAttachments();

  }

  // process all participants for samples
  for (size_t i = 0; i < maxVoiceCards; ++i) {
    const Slot *slot = &snap.slots[i];
    if (slot->participant != nullptr && slot->props.isAllocated) {
      slot->participant->pullSamples(args,
                                     sharedFrames[slot->props.outputDeviceId],
                                     slot->props.cvChannelOffset);
    }
  }


  static constexpr float clipTime = 0.25f;
  processCvRoutes(routes.data(),
                  routes.size(),
                  clipTime,
                  cvChannelOffset,
                  sharedFrames[outputDeviceId].samples,
                  params.data(),
                  inputs.data());

  // cache the VCA levels for the GraphSource inputToOut1 and inputToOut2
  input1Weight = sharedFrames[outputDeviceId].samples[cvChannelOffset + OUT1_CHANNEL];
  input2Weight = sharedFrames[outputDeviceId].samples[cvChannelOffset + OUT2_CHANNEL];

  sendFramesToDevices(sharedFrames, audioPorts.size());

  if (isMidiClockTick) {
    setStatusLight();

    const float lightTime = args.sampleTime * midiPollClockDivider.getDivision();
    const float brightnessDeltaTime = 1 / lightTime;

    // reset all patch usage state to inactive, then selectively activate.
    for (size_t i = 0; i < maxVoiceCards; ++i) {
      lights[CARD_A_PATCH_USAGE_LIGHT + i ].setBrightness(0.f);
    }

    // process all participants for MIDI
    midi::Message midiOutMessage;
    for (size_t i = 0; i < maxVoiceCards; ++i) {
      const Slot *slot = &snap.slots[i];
      if (slot->participant != nullptr && slot->props.isAllocated) {
          lights[CARD_A_PATCH_USAGE_LIGHT + slot->props.slotNum ].setBrightness(0.85f);
          if (slot->participant->pullMidi(args,
                                          midiPollClockDivider.getDivision(),
                                          slot->props.midiChannel,
                                          midiOutMessage)) {
            INFO("frame %" PRId64 ": midi: slot %ld module id %" PRId64 " send message %02X",
                 args.frame, i, slot->participant->getModuleId(), midiOutMessage.getNote());
            midiOutput.sendMidiMessage(midiOutMessage);
          }
      }
      else if (slot->props.hardwareId) {
        lights[CARD_A_PATCH_USAGE_LIGHT + slot->props.slotNum ].setBrightness(0.25f);
      }
    }

    if (buttonMidiController.process(this, midiChannel, midiOutMessage)) {
      midiOutput.sendMidiMessage(midiOutMessage);
    }
    buttonMidiController.updateLights(this);

    out1LevelClipTimer -= lightTime;
    lights[OUT1_LEVEL_CLIP_LIGHT].setBrightnessSmooth(out1LevelClipTimer > 0.f, brightnessDeltaTime);
    out2LevelClipTimer -= lightTime;
    lights[OUT2_LEVEL_CLIP_LIGHT].setBrightnessSmooth(out2LevelClipTimer > 0.f, brightnessDeltaTime);
  }

  if (isGraphPollClockTick &&
      rightExpander.module && rightExpander.module->model == modelOutputInterfaceVisualizer) {
    // Write to visualizer - the expander
    ParticipantGraphMessage *message = static_cast<ParticipantGraphMessage*>(rightExpander.producerMessage);
    message->participantInfoCount = 0;
    message->output1SourceCount = 0;
    message->output2SourceCount = 0;
    message->outputInterfaceInfo.moduleId = getId();
    message->outputInterfaceInfo.slotNum = slotNum;
    message->outputInterfaceInfo.hardwareId = getHardwareId();

    // call each module to get the module's view of ParticipantGraphInfo--
    // this collects all edgges between voice cards (and the external input)
    for (size_t i = 0; i < maxVoiceCards; ++i) {
      const Slot &slot = snap.slots[i];
      if (slot.participant != nullptr && slot.props.isAllocated) {
        // Business section: call each module
        ParticipantGraphInfo info = ParticipantGraphInfo{};
        if (slot.participant->pullGraphInfo(info)) {
          resolveGraphSource(snap, info.source1);
          resolveGraphSource(snap, info.source2);

          if (message->participantInfoCount < maxVoiceCards) {
            message->participantInfos[message->participantInfoCount++] = info;
          }
          else {
            WARN("participantInfos: maxVoiceCards reached");
          }
        }

      }
    }
    // collect all edges to the outputs for the output module
    for (int i = 0; i < maxVoiceCards; ++i) {
      if (params[CARD_A_MIX1_OUTPUT_BUTTON_PARAM + i].getValue()) {
        GraphSource inputToOut1 = makeOutputGraphSource(snap, i, GraphPort::OUT1, input1Weight);
        if (message->output1SourceCount < maxVoiceCards) {
          message->output1Sources[message->output1SourceCount++] = inputToOut1;
        }
        else {
          WARN("output1Sources: maxVoiceCards reached");
        }
      }
      if (params[CARD_A_MIX2_OUTPUT_BUTTON_PARAM + i].getValue()) {
        GraphSource inputToOut2 = makeOutputGraphSource(snap, i, GraphPort::OUT2, input2Weight);
        if (message->output2SourceCount < maxVoiceCards) {
          message->output2Sources[message->output2SourceCount++] = inputToOut2;
        }
        else {
          WARN("output2Sources: maxVoiceCards reached");
        }

      }
    }
    rightExpander.messageFlipRequested = true;
  }
}




/** getCardHardwareId
 * return the hardware Id of this card.
 * This must match the numeric identifier the Pi has in the etc/zoxnoxiousd.cfg file.
 * If it doesn't match ZoxnoxiousControlMsg will not have a channel assignment for this card.
 */
static const uint8_t hardwareId = 0x07;
uint8_t OutputInterface::getHardwareId() {
  return hardwareId;
}


void OutputInterface::setStatusLight() {
  if (discoveryReportReceived) {  // green
    lights[HARDWARE_LINK_LIGHT + 0].setBrightness(0.f);
    lights[HARDWARE_LINK_LIGHT + 1].setBrightness(0.5f);
    lights[HARDWARE_LINK_LIGHT + 2].setBrightness(0.f);
  }
  /* yellow case
     else if (validRightExpander) {
     lights[HARDWARE_LINK_LIGHT + 0].setBrightness(1.f);
     lights[HARDWARE_LINK_LIGHT + 1].setBrightness(1.f);
     lights[HARDWARE_LINK_LIGHT + 2].setBrightness(0.f);
     }
  */
  else {  // red
    lights[HARDWARE_LINK_LIGHT + 0].setBrightness(1.f);
    lights[HARDWARE_LINK_LIGHT + 1].setBrightness(0.f);
    lights[HARDWARE_LINK_LIGHT + 2].setBrightness(0.f);
  }

}

static const uint8_t midiManufacturerId = 0x7d;
static const uint8_t midiSysexDiscoveryReport = 0x01;


void OutputInterface::processMidiInMessage(const midi::Message &msg) {
  // the only thing being processed as of now is the Discovery Report
  INFO("processing MIDI message");
  if (msg.getStatus() == 0xf && msg.getSize() > 3 && msg.bytes[1] == midiManufacturerId) {
    if (msg.bytes[2] == midiSysexDiscoveryReport) {
      processDiscoveryReport(msg);
    }
    else {
      INFO("sysex: unknown");
    }
  }
}


/** processDiscoveryReport
 *
 * read the report on which cards are present in the system.  The
 * MIDI sysex format for this is 28 bytes:
 * 0xF0
 * 0x7D
 * 0x01 -- discovery report
 * 0x?? -- cardA id
 * 0x?? -- cardA channel offset
 * 0x?? -- cardA device id
 * 0x?? -- cardB id
 * 0x?? -- cardB channel offset
 * 0x?? -- cardB device id
 * 0x?? -- cardC id
 * 0x?? -- cardC channel offset
 * 0x?? -- cardC device id
 * 0x?? -- cardD id
 * 0x?? -- cardD channel offset
 * 0x?? -- cardD device id
 * 0x?? -- cardE id
 * 0x?? -- cardE channel offset
 * 0x?? -- cardE device id
 * 0x?? -- cardF id
 * 0x?? -- cardF channel offset
 * 0x?? -- cardF device id
 * 0x?? -- cardG id
 * 0x?? -- cardG channel offset
 * 0x?? -- cardG device id
 * 0x?? -- cardH id
 * 0x?? -- cardH channel offset
 * 0x?? -- cardH device id
 * 0xF7
 * if the card Id isn't 0x00 or 0xFF then process it.
 * This report specifies exactly what cards are present in the
 * system and how the host (VCV Rack) is to communicate with each card.
 * Yes, the report does specify 8 cards.  One is the backplane (this module),
 * the hardware guarantees only six are populated (hardware does not have a 7th slot)
 * but it's there in the report anyway.  Only six are cold-swappable voice cards.
 */

static constexpr int discoveryReportMessageSize = 28;
static constexpr int numReportsCards = 8;

// to be mapped to ParticipantProperty
struct DiscoveredCard {
  uint8_t hardwareId;
  int8_t cvChannelOffset;
  int8_t outputDeviceId;
  int8_t slotNum;
  bool valid;
};


void OutputInterface::processDiscoveryReport(const midi::Message &msg) {
  constexpr int byteOffset = 3; // actual data starts at this offset after sysex header
  int msgSize = msg.getSize(); // cache

  if (discoveryReportReceived == true) {
    INFO("ignoring duplicate Discovery Report");
    return;
  }

  if (msgSize != discoveryReportMessageSize) {
    WARN("Discovery report contains %d bytes, expected %d", msgSize, discoveryReportMessageSize);
  }

  DiscoveredCard cards[numReportsCards] = {};

  // first pass: just parse.  These are in slot order, so i == slot
  for (int8_t i = 0; i < numReportsCards; ++i) {
    int base = byteOffset + (i * 3);
    uint8_t hwId = msg.bytes[base];
    int8_t cvOffset = msg.bytes[base + 1];
    int8_t outputDev = msg.bytes[base + 2];

    // 0x00 and 0xFF are not valid hardware Ids
    if (hwId != 0x00 && hwId != 0xFF) {
      cards[i] = { hwId, cvOffset, outputDev, i, true };
    }
    else {
      cards[i] = { 0, 0, 0, i, false };
    }

  }

  // second pass: apply bizrules
  applyDiscoveryReport(cards);
  discoveryReportReceived = true;
}


// note the midi channel is assigned here.  By convention with the zoxnoxiousd daemon
// the first in the report has channel 0, then 1, etc.
// "Discovered card number maps to MIDI channel number.  Not actual slot number."
void OutputInterface::applyDiscoveryReport(DiscoveredCard *cards) {
  int assignedMidiChannel = 0;
  ParticipantProperty deviceTree[maxVoiceCards] = {};

  for (int i = 0; i < numReportsCards; ++i) {
    const DiscoveredCard& card = cards[i];

    if (!card.valid) {
      continue; // ignore it
    }

    if (card.hardwareId == getHardwareId()) {
      // Backplane
      cvChannelOffset = card.cvChannelOffset;
      outputDeviceId = card.outputDeviceId;
      midiChannel = assignedMidiChannel++;
      slotNum = card.slotNum;
    }
    else if (card.slotNum >= 0 && card.slotNum < maxVoiceCards) {
      // Voice card
      ParticipantProperty& slot = deviceTree[ card.slotNum ];
      slot.moduleId = -1;
      slot.hardwareId = card.hardwareId;
      slot.cvChannelOffset = card.cvChannelOffset;
      slot.outputDeviceId = card.outputDeviceId;
      slot.midiChannel = assignedMidiChannel++;
      slot.slotNum = card.slotNum;
      slot.isAllocated = false;
      INFO("registered hardware id %d midi channel %d", slot.hardwareId, slot.midiChannel);
    }
    else {
      WARN("too many voice cards");
    }

  }

  broker.registerDevices(deviceTree, maxVoiceCards);
}



// send all audio frames to the audio ports
void OutputInterface::sendFramesToDevices(rack::dsp::Frame<maxAudioChannels> *sharedFrame, int numFrames) {
  for (int deviceNum = 0; deviceNum < numFrames; ++deviceNum) {
    if (!audioPorts[deviceNum]->engineInputBuffer.full()) {
      audioPorts[deviceNum]->engineInputBuffer.push(sharedFrame[deviceNum]);
    }
  }
}





json_t* OutputInterface::dataToJson() {
  json_t* rootJ = json_object();
  json_object_set_new(rootJ, "midiInput", midiInput.toJson());
  json_object_set_new(rootJ, "midiOutput", midiOutput.toJson());
  for (std::size_t deviceNum = 0; deviceNum < audioPorts.size(); ++deviceNum) {
    std::string thisAudioPortNum = audioPortNum + std::to_string(deviceNum);
    json_object_set_new(rootJ, thisAudioPortNum.c_str(), audioPorts[deviceNum]->toJson());
  }

  return rootJ;
}

void OutputInterface::dataFromJson(json_t* rootJ) {
  json_t* midiInputJ = json_object_get(rootJ, "midiInput");
  if (midiInputJ) {
    midiInput.fromJson(midiInputJ);
  }

  json_t* midiOutputJ = json_object_get(rootJ, "midiOutput");
  if (midiOutputJ) {
    midiOutput.fromJson(midiOutputJ);
  }

  for (std::size_t deviceNum = 0; deviceNum < audioPorts.size(); ++deviceNum) {
    std::string thisAudioPortNum = audioPortNum + std::to_string(deviceNum);
    json_t* audioPortJ = json_object_get(rootJ, thisAudioPortNum.c_str());
    if (audioPortJ) {
      audioPorts[deviceNum]->fromJson(audioPortJ);
    }
  }

}



bool OutputInterface::isPrimary() const {
    return OutputInterface::instance.load(std::memory_order_relaxed) == this;
}


void OutputInterface::serviceParticipantAttachments() {

  for (int64_t moduleId : APP->engine->getModuleIds()) {
    Module *m = APP->engine->getModule(moduleId);
    auto* p = dynamic_cast<ParticipantAdapter*>(m);
    if (!p) {
      continue;
    }

    auto& lifecycle = p->getLifecycle();

    if (!p->getParticipant()) {
      WARN("ParticipantAdapter points to null participant");
      continue;
    }
    if (lifecycle.wantAttach()) {
      INFO("completing attach for module %" PRId64, moduleId);
      if (lifecycle.completeAttach(&broker, p->getParticipant())) {
        p->onAttach();
      }
    }
  }
}

//--------------------
// ModuleWidget / UI
//--------------------

struct OutputInterfaceWidget : ModuleWidget {
  OutputInterfaceWidget(OutputInterface* module) :
    outputA1Text(nullptr), outputA2Text(nullptr),
    outputB1Text(nullptr), outputB2Text(nullptr),
    outputC1Text(nullptr), outputC2Text(nullptr),
    outputD1Text(nullptr), outputD2Text(nullptr),
    outputE1Text(nullptr), outputE2Text(nullptr),
    outputF1Text(nullptr), outputF2Text(nullptr) {
    setModule(module);
    setPanel(createPanel(asset::plugin(pluginInstance, "res/OutputInterface.svg")));

    if (module != nullptr) {
      Broker& b = module->getBroker();
      const std::shared_ptr<HardwareNameService> hns = b.getHardwareNameService();
      if (hns) {
        outputA1Text = hns->getShortNamePtr(0);
        outputA2Text = hns->getShortNamePtr(1);
        outputB1Text = hns->getShortNamePtr(2);
        outputB2Text = hns->getShortNamePtr(3);
        outputC1Text = hns->getShortNamePtr(4);
        outputC2Text = hns->getShortNamePtr(5);
        outputD1Text = hns->getShortNamePtr(6);
        outputD2Text = hns->getShortNamePtr(7);
        outputE1Text = hns->getShortNamePtr(8);
        outputE2Text = hns->getShortNamePtr(9);
        outputF1Text = hns->getShortNamePtr(10);
        outputF2Text = hns->getShortNamePtr(11);
      }
    }

    addChild(createWidget<ScrewSlottedKnurled>(Vec(RACK_GRID_WIDTH, 0)));
    addChild(createWidget<ScrewSlottedKnurled>(Vec(box.size.x - 2 * RACK_GRID_WIDTH, 0)));
    addChild(createWidget<ScrewSlottedKnurled>(Vec(RACK_GRID_WIDTH, RACK_GRID_HEIGHT - RACK_GRID_WIDTH)));
    addChild(createWidget<ScrewSlottedKnurled>(Vec(box.size.x - 2 * RACK_GRID_WIDTH, RACK_GRID_HEIGHT - RACK_GRID_WIDTH)));

    addChild(createLightCentered<SmallLight<RedGreenBlueLight>>(mm2px(Vec(53.022, 14.198)), module, OutputInterface::HARDWARE_LINK_LIGHT));

    addChild(createLightCentered<SmallLight<ZoxAmberLight>>(mm2px(Vec(10.475, 21.639)), module, OutputInterface::CARD_A_PATCH_USAGE_LIGHT));
    addChild(createLightCentered<SmallLight<ZoxAmberLight>>(mm2px(Vec(17.034, 21.639)), module, OutputInterface::CARD_B_PATCH_USAGE_LIGHT));
    addChild(createLightCentered<SmallLight<ZoxAmberLight>>(mm2px(Vec(23.594, 21.639)), module, OutputInterface::CARD_C_PATCH_USAGE_LIGHT));
    addChild(createLightCentered<SmallLight<ZoxAmberLight>>(mm2px(Vec(30.153, 21.639)), module, OutputInterface::CARD_D_PATCH_USAGE_LIGHT));
    addChild(createLightCentered<SmallLight<ZoxAmberLight>>(mm2px(Vec(36.712, 21.639)), module, OutputInterface::CARD_E_PATCH_USAGE_LIGHT));
    addChild(createLightCentered<SmallLight<ZoxAmberLight>>(mm2px(Vec(43.272, 21.639)), module, OutputInterface::CARD_F_PATCH_USAGE_LIGHT));


    addParam(createLightParamCentered<ZPushButtonSmallStatefulLightLatch<TinyLight<ZoxAmberLight>>>(mm2px(Vec(29.665, 39.243)), module, OutputInterface::CARD_A_MIX1_OUTPUT_BUTTON_PARAM, OutputInterface::CARD_A_MIX1_OUTPUT_BUTTON_LIGHT));
    addParam(createLightParamCentered<ZPushButtonSmallStatefulLightLatch<TinyLight<ZoxAmberLight>>>(mm2px(Vec(64.674, 39.421)), module, OutputInterface::CARD_A_MIX2_OUTPUT_BUTTON_PARAM, OutputInterface::CARD_A_MIX2_OUTPUT_BUTTON_LIGHT));
    addParam(createLightParamCentered<ZPushButtonSmallStatefulLightLatch<TinyLight<ZoxAmberLight>>>(mm2px(Vec(29.665, 44.56)), module, OutputInterface::CARD_B_MIX1_OUTPUT_BUTTON_PARAM, OutputInterface::CARD_B_MIX1_OUTPUT_BUTTON_LIGHT));
    addParam(createLightParamCentered<ZPushButtonSmallStatefulLightLatch<TinyLight<ZoxAmberLight>>>(mm2px(Vec(64.674, 44.702)), module, OutputInterface::CARD_B_MIX2_OUTPUT_BUTTON_PARAM, OutputInterface::CARD_B_MIX2_OUTPUT_BUTTON_LIGHT));
    addParam(createLightParamCentered<ZPushButtonSmallStatefulLightLatch<TinyLight<ZoxAmberLight>>>(mm2px(Vec(29.66, 49.876)), module, OutputInterface::CARD_C_MIX1_OUTPUT_BUTTON_PARAM, OutputInterface::CARD_C_MIX1_OUTPUT_BUTTON_LIGHT));
    addParam(createLightParamCentered<ZPushButtonSmallStatefulLightLatch<TinyLight<ZoxAmberLight>>>(mm2px(Vec(64.674, 49.983)), module, OutputInterface::CARD_C_MIX2_OUTPUT_BUTTON_PARAM, OutputInterface::CARD_C_MIX2_OUTPUT_BUTTON_LIGHT));
    addParam(createLightParamCentered<ZPushButtonSmallStatefulLightLatch<TinyLight<ZoxAmberLight>>>(mm2px(Vec(29.665, 55.193)), module, OutputInterface::CARD_D_MIX1_OUTPUT_BUTTON_PARAM, OutputInterface::CARD_D_MIX1_OUTPUT_BUTTON_LIGHT));
    addParam(createLightParamCentered<ZPushButtonSmallStatefulLightLatch<TinyLight<ZoxAmberLight>>>(mm2px(Vec(64.674, 55.264)), module, OutputInterface::CARD_D_MIX2_OUTPUT_BUTTON_PARAM, OutputInterface::CARD_D_MIX2_OUTPUT_BUTTON_LIGHT));
    addParam(createLightParamCentered<ZPushButtonSmallStatefulLightLatch<TinyLight<ZoxAmberLight>>>(mm2px(Vec(29.665, 60.51)), module, OutputInterface::CARD_E_MIX1_OUTPUT_BUTTON_PARAM, OutputInterface::CARD_E_MIX1_OUTPUT_BUTTON_LIGHT));
    addParam(createLightParamCentered<ZPushButtonSmallStatefulLightLatch<TinyLight<ZoxAmberLight>>>(mm2px(Vec(64.674, 60.545)), module, OutputInterface::CARD_E_MIX2_OUTPUT_BUTTON_PARAM, OutputInterface::CARD_E_MIX2_OUTPUT_BUTTON_LIGHT));
    addParam(createLightParamCentered<ZPushButtonSmallStatefulLightLatch<TinyLight<ZoxAmberLight>>>(mm2px(Vec(29.665, 65.826)), module, OutputInterface::CARD_F_MIX1_OUTPUT_BUTTON_PARAM, OutputInterface::CARD_F_MIX1_OUTPUT_BUTTON_LIGHT));
    addParam(createLightParamCentered<ZPushButtonSmallStatefulLightLatch<TinyLight<ZoxAmberLight>>>(mm2px(Vec(64.674, 65.826)), module, OutputInterface::CARD_F_MIX2_OUTPUT_BUTTON_PARAM, OutputInterface::CARD_F_MIX2_OUTPUT_BUTTON_LIGHT));


    addParam(createParamCentered<ZoxSlider>(mm2px(Vec(17.28, 89.244)), module, OutputInterface::OUT1_LEVEL_KNOB_PARAM));
    addParam(createParamCentered<ZoxSlider>(mm2px(Vec(52.11, 89.244)), module, OutputInterface::OUT2_LEVEL_KNOB_PARAM));


    addInput(createInputCentered<BNCPort>(mm2px(Vec(17.303, 108.604)), module, OutputInterface::OUT1_LEVEL_INPUT));
    addInput(createInputCentered<BNCPort>(mm2px(Vec(52.11, 108.604)), module, OutputInterface::OUT2_LEVEL_INPUT));


    // mm2px(Vec(22.0, 3.636))
    cardAOutput1TextField = createWidget<CardTextDisplay>(mm2px(Vec(8.645, 37.603)));
    cardAOutput1TextField->setNumChars(10);
    cardAOutput1TextField->box.size = (mm2px(Vec(18.0, 3.636)));
    cardAOutput1TextField->setText(outputA1Text);
    addChild(cardAOutput1TextField);

    // mm2px(Vec(18.0, 3.636))
    cardAOutput2TextField = createWidget<CardTextDisplay>(mm2px(Vec(43.705, 37.603)));
    cardAOutput2TextField->setNumChars(10);
    cardAOutput2TextField->box.size = (mm2px(Vec(18.0, 3.636)));
    cardAOutput2TextField->setText(outputA2Text);
    addChild(cardAOutput2TextField);

    // mm2px(Vec(18.0, 3.636))
    cardBOutput1TextField = createWidget<CardTextDisplay>(mm2px(Vec(8.645, 42.884)));
    cardBOutput1TextField->setNumChars(10);
    cardBOutput1TextField->box.size = (mm2px(Vec(18.0, 3.636)));
    cardBOutput1TextField->setText(outputB1Text);
    addChild(cardBOutput1TextField);

    // mm2px(Vec(18.0, 3.636))
    cardBOutput2TextField = createWidget<CardTextDisplay>(mm2px(Vec(43.705, 42.884)));
    cardBOutput2TextField->setNumChars(10);
    cardBOutput2TextField->box.size = (mm2px(Vec(18.0, 3.636)));
    cardBOutput2TextField->setText(outputB2Text);
    addChild(cardBOutput2TextField);

    // mm2px(Vec(18.0, 3.636))
    cardCOutput1TextField = createWidget<CardTextDisplay>(mm2px(Vec(8.645, 48.165)));
    cardCOutput1TextField->setNumChars(10);
    cardCOutput1TextField->box.size = (mm2px(Vec(18.0, 3.636)));
    cardCOutput1TextField->setText(outputC1Text);
    addChild(cardCOutput1TextField);

    // mm2px(Vec(18.0, 3.636))
    cardCOutput2TextField = createWidget<CardTextDisplay>(mm2px(Vec(43.705, 48.165)));
    cardCOutput2TextField->setNumChars(10);
    cardCOutput2TextField->box.size = (mm2px(Vec(18.0, 3.636)));
    cardCOutput2TextField->setText(outputC2Text);
    addChild(cardCOutput2TextField);


    // mm2px(Vec(18.0, 3.636))
    cardDOutput1TextField = createWidget<CardTextDisplay>(mm2px(Vec(8.645, 53.446)));
    cardDOutput1TextField->setNumChars(10);
    cardDOutput1TextField->box.size = (mm2px(Vec(18.0, 3.636)));
    cardDOutput1TextField->setText(outputD1Text);
    addChild(cardDOutput1TextField);

    // mm2px(Vec(18.0, 3.636))
    cardDOutput2TextField = createWidget<CardTextDisplay>(mm2px(Vec(43.705, 53.446)));
    cardDOutput2TextField->setNumChars(10);
    cardDOutput2TextField->box.size = (mm2px(Vec(18.0, 3.636)));
    cardDOutput2TextField->setText(outputD2Text);
    addChild(cardDOutput2TextField);

    // mm2px(Vec(18.0, 3.636))
    cardEOutput1TextField = createWidget<CardTextDisplay>(mm2px(Vec(8.645, 58.727)));
    cardEOutput1TextField->setNumChars(10);
    cardEOutput1TextField->box.size = (mm2px(Vec(18.0, 3.636)));
    cardEOutput1TextField->setText(outputE1Text);
    addChild(cardEOutput1TextField);

    // mm2px(Vec(18.0, 3.636))
    cardEOutput2TextField = createWidget<CardTextDisplay>(mm2px(Vec(43.705, 58.727)));
    cardEOutput2TextField->setNumChars(10);
    cardEOutput2TextField->box.size = (mm2px(Vec(18.0, 3.636)));
    cardEOutput2TextField->setText(outputE2Text);
    addChild(cardEOutput2TextField);

    // mm2px(Vec(18.0, 3.636))
    cardFOutput1TextField = createWidget<CardTextDisplay>(mm2px(Vec(8.645, 64.008)));
    cardFOutput1TextField->setNumChars(10);
    cardFOutput1TextField->box.size = (mm2px(Vec(18.0, 3.636)));
    cardFOutput1TextField->setText(outputF1Text);
    addChild(cardFOutput1TextField);

    // mm2px(Vec(18.0, 3.636))
    cardFOutput2TextField = createWidget<CardTextDisplay>(mm2px(Vec(43.705, 64.008)));
    cardFOutput2TextField->setNumChars(10);
    cardFOutput2TextField->box.size = (mm2px(Vec(18.0, 3.636)));
    cardFOutput2TextField->setText(outputF2Text);
    addChild(cardFOutput2TextField);

  }


  void appendContextMenu(Menu *menu) override {
    OutputInterface *module = dynamic_cast<OutputInterface*>(this->module);
    if (!module) {
      return;
    }

    menu->addChild(new MenuSeparator);

    menu->addChild(createSubmenuItem("Hardware", "",
        [=](Menu* menu) {
          menu->addChild(createMenuItem("Scan now", "",
                           [=]() {
                             module->hardwareDiscovery.discover(
                               module->midiInput,
                               module->midiOutput,
                               *module->audioPorts[0]);
                           }));

          menu->addChild(new MenuSeparator);

          menu->addChild(createSubmenuItem("MIDI Out Device", "",
                                           [=](Menu* menu) {
                                             appendMidiMenu(menu, &module->midiOutput);
                                           }));
          menu->addChild(createSubmenuItem("MIDI In Device", "",
                                           [=](Menu* menu) {
                                             appendMidiMenu(menu, &module->midiInput);
                                           }));

          if (module->audioPorts.size() == 1) {
            menu->addChild(createSubmenuItem("Audio Device", "",
                                             [=](Menu* menu) {
                                               appendAudioMenu(menu, module->audioPorts[0]);
                                             }));
          }
          else {
            menu->addChild(createSubmenuItem("Audio Device 0", "",
                                             [=](Menu* menu) {
                                               appendAudioMenu(menu, module->audioPorts[0]);
                                             }));
            menu->addChild(createSubmenuItem("Audio Device 1", "",
                                             [=](Menu* menu) {
                                               appendAudioMenu(menu, module->audioPorts[1]);
                                             }));
          }
        }));

    menu->addChild(new MenuSeparator);

    InstantiateExpanderItem *expanderItem = createMenuItem<InstantiateExpanderItem>("Add visualizer (right side)", "");
    expanderItem->module = module;
    expanderItem->model = modelOutputInterfaceVisualizer;
    expanderItem->posit = box.pos;
    expanderItem->posit.x += box.size.x;
    menu->addChild(expanderItem);

    menu->addChild(new MenuSeparator);

    menu->addChild(createMenuItem("Autotune", "", [=]() {
          module->midiOutput.sendMidiMessage(module->MIDI_TUNE_REQUEST);
        }));

    menu->addChild(new MenuSeparator);

    menu->addChild(createSubmenuItem("System", "",
        [=](Menu* menu) {
          menu->addChild(createSubmenuItem("Restart", "",
                                           [=](Menu* menu) {
                                             menu->addChild(createMenuItem("Restart now", "", [=]() {
                                               module->midiOutput.sendMidiMessage(
                                                 module->MIDI_RESTART_SYSEX);
                                             }));
                                           }));

          menu->addChild(createSubmenuItem("Shutdown", "",
                                           [=](Menu* menu) {
                                             menu->addChild(createMenuItem("Shut down now", "", [=]() {
                                               module->midiOutput.sendMidiMessage(
                                                 module->MIDI_SHUTDOWN_SYSEX);
                                             }));
                                           }));
        }));
  }

  CardTextDisplay *cardAOutput1TextField;
  CardTextDisplay *cardAOutput2TextField;
  const std::string *outputA1Text;
  const std::string *outputA2Text;

  CardTextDisplay *cardBOutput1TextField;
  CardTextDisplay *cardBOutput2TextField;
  const std::string *outputB1Text;
  const std::string *outputB2Text;

  CardTextDisplay *cardCOutput1TextField;
  CardTextDisplay *cardCOutput2TextField;
  const std::string *outputC1Text;
  const std::string *outputC2Text;

  CardTextDisplay *cardDOutput1TextField;
  CardTextDisplay *cardDOutput2TextField;
  const std::string *outputD1Text;
  const std::string *outputD2Text;

  CardTextDisplay *cardEOutput1TextField;
  CardTextDisplay *cardEOutput2TextField;
  const std::string *outputE1Text;
  const std::string *outputE2Text;

  CardTextDisplay *cardFOutput1TextField;
  CardTextDisplay *cardFOutput2TextField;
  const std::string *outputF1Text;
  const std::string *outputF2Text;
};


const std::string OutputInterface::audioPortNum = "audioPort";

// see Zoxnoxious MIDI spec for details

const midi::Message OutputInterface::MIDI_DISCOVERY_REQUEST_SYSEX = []{
  midi::Message m;
  m.bytes = { 0xF0, 0x7D, 0x02, 0xF7 };
  return m;
}();

const midi::Message OutputInterface::MIDI_SHUTDOWN_SYSEX = []{
  midi::Message m;
  m.bytes = { 0xF0, 0x7D, 0x03, 0xF7 };
  return m;
}();

const midi::Message OutputInterface::MIDI_RESTART_SYSEX = []{
  midi::Message m;
  m.bytes = { 0xF0, 0x7D, 0x04, 0xF7 };
  return m;
}();

const midi::Message OutputInterface::MIDI_TUNE_REQUEST = []{
  midi::Message m;
  m.bytes = { 0xF6 };
  return m;
}();


const std::vector<ButtonMapping<OutputInterface> > OutputInterface::buttonMappings = {
    { CARD_A_MIX1_OUTPUT_BUTTON_PARAM, CARD_A_MIX1_OUTPUT_BUTTON_LIGHT, { 0, 1} },
    { CARD_B_MIX1_OUTPUT_BUTTON_PARAM, CARD_B_MIX1_OUTPUT_BUTTON_LIGHT, { 2, 3} },
    { CARD_C_MIX1_OUTPUT_BUTTON_PARAM, CARD_C_MIX1_OUTPUT_BUTTON_LIGHT, { 4, 5} },
    { CARD_D_MIX1_OUTPUT_BUTTON_PARAM, CARD_D_MIX1_OUTPUT_BUTTON_LIGHT, { 6, 7} },
    { CARD_E_MIX1_OUTPUT_BUTTON_PARAM, CARD_E_MIX1_OUTPUT_BUTTON_LIGHT, { 8, 9} },
    { CARD_F_MIX1_OUTPUT_BUTTON_PARAM, CARD_F_MIX1_OUTPUT_BUTTON_LIGHT, { 10, 11} },
    { CARD_A_MIX2_OUTPUT_BUTTON_PARAM, CARD_A_MIX2_OUTPUT_BUTTON_LIGHT, { 12, 13} },
    { CARD_B_MIX2_OUTPUT_BUTTON_PARAM, CARD_B_MIX2_OUTPUT_BUTTON_LIGHT, { 14, 15} },
    { CARD_C_MIX2_OUTPUT_BUTTON_PARAM, CARD_C_MIX2_OUTPUT_BUTTON_LIGHT, { 16, 17} },
    { CARD_D_MIX2_OUTPUT_BUTTON_PARAM, CARD_D_MIX2_OUTPUT_BUTTON_LIGHT, { 18, 19} },
    { CARD_E_MIX2_OUTPUT_BUTTON_PARAM, CARD_E_MIX2_OUTPUT_BUTTON_LIGHT, { 20, 21} },
    { CARD_F_MIX2_OUTPUT_BUTTON_PARAM, CARD_F_MIX2_OUTPUT_BUTTON_LIGHT, { 22, 23} }
};


} // namespace zox

Model* modelOutputInterface = createModel<zox::OutputInterface, zox::OutputInterfaceWidget>("OutputInterface");
