brer-rabbit/zoxnoxious/vcv_rack/src/OutputInterface.hpp

#pragma once

#include <array>
#include <atomic>
#include "Participant.hpp"
#include "ParticipantAdapter.hpp"
#include "AudioMidi.hpp"
#include "HardwareDiscovery.hpp"
#include "modulehelpers.hpp"

namespace zox {

// primary stuff:

struct DiscoveredCard;

// message that gets passed to expander interface to visualizer
struct ParticipantGraphMessage {
  ParticipantGraphInfo participantInfos[maxVoiceCards];
  size_t participantInfoCount = 0;

  ParticipantGraphInfo outputInterfaceInfo;

  GraphSource output1Sources[maxVoiceCards];
  size_t output1SourceCount = 0;

  GraphSource output2Sources[maxVoiceCards];
  size_t output2SourceCount = 0;
};

struct OutputInterface final : rack::engine::Module {
  enum ParamId {
    OUT1_LEVEL_KNOB_PARAM,
    OUT2_LEVEL_KNOB_PARAM,
    // the MIX1 and MIX2 enums need to be sequential
    CARD_A_MIX1_OUTPUT_BUTTON_PARAM,
    CARD_B_MIX1_OUTPUT_BUTTON_PARAM,
    CARD_C_MIX1_OUTPUT_BUTTON_PARAM,
    CARD_D_MIX1_OUTPUT_BUTTON_PARAM,
    CARD_E_MIX1_OUTPUT_BUTTON_PARAM,
    CARD_F_MIX1_OUTPUT_BUTTON_PARAM,
    CARD_A_MIX2_OUTPUT_BUTTON_PARAM,
    CARD_B_MIX2_OUTPUT_BUTTON_PARAM,
    CARD_C_MIX2_OUTPUT_BUTTON_PARAM,
    CARD_D_MIX2_OUTPUT_BUTTON_PARAM,
    CARD_E_MIX2_OUTPUT_BUTTON_PARAM,
    CARD_F_MIX2_OUTPUT_BUTTON_PARAM,
    PARAMS_LEN
  };
  enum InputId {
    OUT1_LEVEL_INPUT,
    OUT2_LEVEL_INPUT,
    INPUTS_LEN
  };
  enum OutputId {
    OUTPUTS_LEN
  };
  enum LightId {
    OUT1_LEVEL_CLIP_LIGHT,
    OUT2_LEVEL_CLIP_LIGHT,
    // the MIX1 and MIX2 enums need to be sequential
    CARD_A_MIX1_OUTPUT_BUTTON_LIGHT,
    CARD_B_MIX1_OUTPUT_BUTTON_LIGHT,
    CARD_C_MIX1_OUTPUT_BUTTON_LIGHT,
    CARD_D_MIX1_OUTPUT_BUTTON_LIGHT,
    CARD_E_MIX1_OUTPUT_BUTTON_LIGHT,
    CARD_F_MIX1_OUTPUT_BUTTON_LIGHT,
    CARD_A_MIX2_OUTPUT_BUTTON_LIGHT,
    CARD_B_MIX2_OUTPUT_BUTTON_LIGHT,
    CARD_C_MIX2_OUTPUT_BUTTON_LIGHT,
    CARD_D_MIX2_OUTPUT_BUTTON_LIGHT,
    CARD_E_MIX2_OUTPUT_BUTTON_LIGHT,
    CARD_F_MIX2_OUTPUT_BUTTON_LIGHT,
    CARD_A_PATCH_USAGE_LIGHT,
    CARD_B_PATCH_USAGE_LIGHT,
    CARD_C_PATCH_USAGE_LIGHT,
    CARD_D_PATCH_USAGE_LIGHT,
    CARD_E_PATCH_USAGE_LIGHT,
    CARD_F_PATCH_USAGE_LIGHT,
    ENUMS(HARDWARE_LINK_LIGHT, 3),
    LIGHTS_LEN
  };


  OutputInterface();
  ~OutputInterface();

  // Global access point: no writes allowed from the audio thread
  static std::atomic<OutputInterface*> instance;

  // Broker access
  Broker& getBroker() { return broker; }


  // Module methods
  void onAdd(const AddEvent &e) override;
  void onRemove(const RemoveEvent &e) override;
  void onReset() override;
  void onSampleRateChange(const SampleRateChangeEvent& e) override;
  void process(const ProcessArgs& args) override;

  json_t* dataToJson() override;
  void dataFromJson(json_t* rootJ) override;

  std::vector<ZoxnoxiousAudioPort*> audioPorts;
  ZoxnoxiousMidiOutput midiOutput;
  midi::InputQueue midiInput;

  // Discovery related variables
  static const midi::Message MIDI_DISCOVERY_REQUEST_SYSEX;
  static const midi::Message MIDI_SHUTDOWN_SYSEX;
  static const midi::Message MIDI_RESTART_SYSEX;
  static const midi::Message MIDI_TUNE_REQUEST;

  bool isPrimary() const;

  HardwareDiscovery hardwareDiscovery;

private:
  Broker broker;

  float out1LevelClipTimer;
  float out2LevelClipTimer;

  static const std::vector<ButtonMapping<OutputInterface> > buttonMappings;
  std::vector<ButtonState> buttonStates;
  ButtonMidiController<OutputInterface> buttonMidiController;

  uint8_t getHardwareId();
  void setStatusLight();
  int8_t cvChannelOffset;
  int8_t outputDeviceId;
  int8_t midiChannel;
  int8_t slotNum;

  bool discoveryReportReceived = false;
  dsp::ClockDivider orchestrationClockDivider;
  dsp::ClockDivider midiPollClockDivider;
  dsp::ClockDivider graphPollClockDivider;

  void processMidiInMessage(const midi::Message &msg);
  void processDiscoveryReport(const midi::Message &msg);
  void applyDiscoveryReport(DiscoveredCard *cards);

  void sendFramesToDevices(rack::dsp::Frame<maxAudioChannels> *sharedFrame, int numFrames);

  void serviceParticipantAttachments();

  std::array<CvRoute,2> routes;

  // graph sources: these will be passed via expander
  ParticipantGraphMessage graphMessages[2];

  void dumpParticipantGraphs() const;

  float input1Weight = 0.f;
  float input2Weight = 0.f;

  static const std::string audioPortNum;
};


} // namespace zox
