brer-rabbit/zoxnoxious/vcv_rack/src/ParticipantAdapter.hpp

#pragma once

#include "Participant.hpp"

namespace zox {

// ParticipantAdapter owns a Participant.  ParticipantAdapter manages lifecycle,
// while Participant defines orchestrator-facing behavior.  An implemented concrete module
// will wire these together
struct ParticipantAdapter : rack::Module {

public:
  ParticipantAdapter();
  virtual ~ParticipantAdapter();

  void setParticipant(Participant* p);
  Participant* getParticipant();
  void process(const ProcessArgs& args) final;

  void onAdd(const AddEvent& e) override;
  void onRemove(const RemoveEvent& e) override;

  ParticipantLifecycle& getLifecycle();

  // override function available for callback on attaching to broker
  virtual void onAttach();

protected:
  ParticipantLifecycle lifecycle;
  Participant* participant;

  // shortcut function that takes the expander light enum to set it based on attached state.
  // May be overridden if you don't want to go with the flow.
  // setLightEnum to be called during initialization, and
  // setAttachedLightStatus gets called during process()
  virtual void setLightEnum(int lightEnum);
  virtual void setAttachedLightStatus();

private:
  rack::dsp::ClockDivider lightDivider;
  int myLightEnum;
};

} // namespace zox
